tobias-liaudat/ClassG_amp/Fuente SW/fuente_negativa/imgs/PCB_neg_f.png

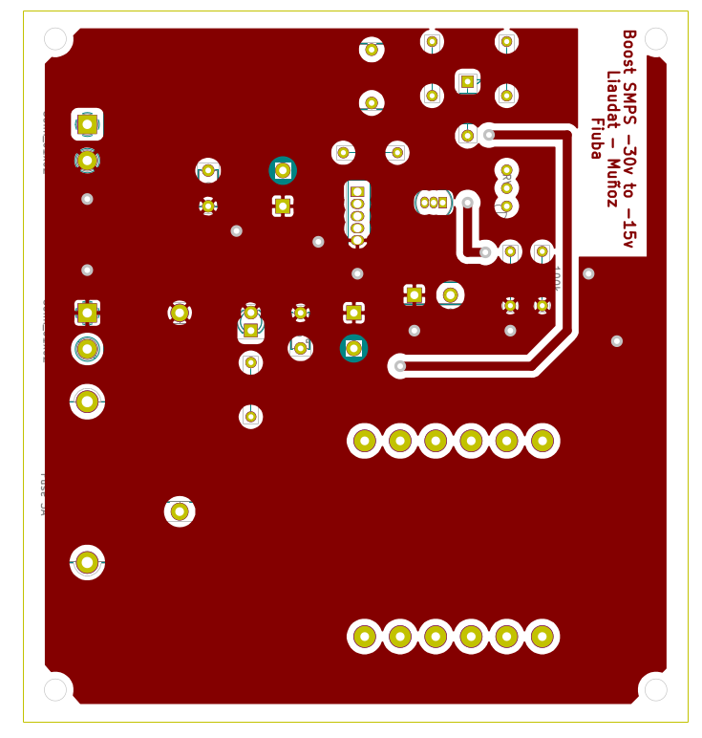
Fuente SW/fuente_negativa/imgs/PCB_neg_f.png
