tobias-liaudat/ClassG_amp/Amplificador/Ajustes_ganancia_alimentacion/ClassG_DEF_v3.asc

C1: cap; 47µ
C2: cap; 0.3n
C3: cap; 100µ
C4: cap; 47µ
C5: cap; 47µ
C6: cap; 100n
C7: cap; 100n
C8: cap; 1m
C9: cap; 30p
C10: cap; 1m
C11: cap; 100n
C12: cap; 47µ
C13: cap; 220µ
C14: cap; 220µ
C15: cap; 100n
C16: cap; 220µ
C17: cap; 220µ
C18: cap; {C_sUp}
D1: diode; 1N4148
D2: diode; 1N4148
D3: diode; 1N4148
D4: diode; 1N4148
D8: zener; D1N4728
D9: zener; D1N4728
D10: diode; 1N4148
D11: diode; 1N4148
D12: diode; dmur860
D13: diode; dmur860
D17: diode; 1N4148
D18: diode; 1N4148
L1: ind; 1µ
m_VA: voltage; {VCC}; Rser=0.1
m_VB: voltage; {VCC1}; Rser=0.1
PR1: res; {PR1}
Q1: pnp; BC856A
Q2: pnp; BC856A
Q3: npn; BC846A
Q4: npn; BC846A
Q5: pnp; BC856A
Q6: pnp; BC856A
Q7: pnp; 2SA1837
Q8: npn; 2SC4793
Q9: npn; BC846A
Q10: npn; BC846A
Q11: npn; 2SC4793
Q14: npn; 2SC4793
Q15: pnp; 2SA1837
Q16: npn; 2SC4793
Q17: pnp; 2SA1837
Q18: npn; 2SC5200
Q19: npn; 2SC5200
Q20: pnp; 2SA1943
Q21: pnp; 2SA1943
Q22: npn; BC846A
Q23: npn; BC846A
Q24: npn; BC846A
Q25: npn; BC846A
Q26: npn; MPSA42
Q27: pnp; MPSA92
R1: res; 100k
R2: res; 10
R3: res; 1.2k
R4: res; 1.2k
R5: res; 100
R6: res; 68
R7: res; 100
R8: res; 68
R9: res; 100
R10: res; 100
R11: res; 2.2k
R12: res; 2.2k
R13: res; 10k
R14: res; 10k
R15: res; 50
R16: res; 2.2k
R17: res; 2.2k
R18: res; 33
R19: res; 10
R20: res; 100
R21: res; 3.3K
R22: res; 390
R23: res; 16
R24: res; 2.2k
R25: res; 2.2k
R26: res; 10
R27: res; 10
R28: res; 100
R29: res; 100
R30: res; 560
R31: res; 180
R32: res; 100
R33: res; 100
R36: res; 100
R37: res; 0.22
R38: res; 2.2k
R39: res; 10
R40: res; 0.22
R41: res; 2.2k
R44: res; 0.01
R45: res; 330
R46: res; 100
R_FB_POT: res; {R_FB_POT}
RL: res; {RL}
S1: sw
V1: signal; SINE(0 {Vi} {freq})
V2: signal; PULSE(-1 10 20m 1n 1n 2m 4m)
VA: voltage; {VCC}; Rser=0.1
VB: voltage; {VCC1}; Rser=0.1
Named nets: 0, Vout, Vin, Vout2, m_VB, VB, VA, m_VA
Proteccion VAS
Degenracion emisor y muestreo para proteccion
VAS
Speedup capacitor
Current protection
Current protection
Vout
.meas tran Pmed_fuentes_neg AVG ((V(m_va)*(I(M_va)))+(V(m_vb)*(I(M_vb))))
.meas tran Pmed_fuentes_pos AVG (V(va)*(-I(Va)))+(V(vb)*(-I(Vb)))
.meas Pmed_F param (Pmed_fuentes_pos + Pmed_fuentes_neg)
Calculo potencias y eficiencia
.meas tran Pmed_RL AVG (V(vout)*(-I(Rl)))
.meas Eff param (Pmed_RL / Pmed_F)
; Simulaciones para las THD 
; .step param Vi list 1.74 1.27
.param Vi 1.0
; .step param freq list 1k 10k 20k
.param freq 1k
.param ciclos=15
.param puntos=10000
.param paso='1/(freq*puntos)' ; paso temporal
.param tf='ciclos/freq + 1m' ; Tiempo final
.tran 0 {tf} 1m {paso} ; Simulacion transient
.four {freq} 40 V(vout) ; Fourier
; .op
; Parametros
.param VCC 50 ; Riel alto
;.step param VCC list  30 40 50; Riel alto
.param VCC1 15 ; Riel bajo
.param PR1 0.22k ;   Pot MultV_BE
; .step param PR1 list 0.58k 0.59k 0.6k
.param R_FB_POT 10.6 ; Feedback R (Gain adjust)
.param RL 8 ; Carga
.param C_sUp 100n ; Cap SpeedUp
; Includes 
.inc D1N4728.mod
.inc DMBR1645.mod
.inc 2SC5200.mod
.inc 2SA1943.mod
.inc MUR860.LIB
.inc MPSA42.mod
.inc MPSA92.mod
.inc D1N5226.mod
.model SW SW()
Potenciometro 100 Ohm , 25 vueltas
Potenciometro 1 kOhm , 25 vueltas
.meas tran P_Q19 AVG((V(n012)-V(n020))*-Ie(Q19))
.meas tran P_Q18 AVG((V(va)-V(n012))*-Ie(Q18))
.meas tran P_Q16 AVG((V(va)-V(n009))*-Ie(Q16))
.meas tran P_Q14 AVG((V(va)-V(n017))*-Ie(Q14))
.meas tran P_Q20 AVG((V(n036)-V(n047))*Ie(Q20))
.meas tran P_Q21 AVG((V(n047)-V(m_VA))*Ie(Q21))
.meas tran P_Q15 AVG((V(n033)-V(m_VA))*Ie(Q15))
.meas tran P_Q17 AVG((V(n048)-V(m_VA))*Ie(Q17))
.meas tran P_Q7 AVG((V(n002)-V(n006))*Ie(Q7))
.meas tran P_Q11 AVG((V(n049)-V(n055))*-Ie(Q11))
.meas tran P_Q8 AVG((V(n013)-V(n018))*-Ie(Q8))
Realimentador
