tobias-liaudat/ClassG_amp/Fuente SW/fuente_positiva/simulacion/step_down_LM2576.asc

C1: polcap; 220µ; V=63 Irms=465m Rser=0.2 Lser=0 mfg="Nichicon" pn="UPR1J221MPH" type="Al electrolytic"
C2: polcap; 220µ; V=63 Irms=1.45 Rser=0.07 Lser=0 mfg="Panasonic" pn="ECA1JFQ471" type="Al electrolytic"
D1: schottky; MBR20100CT
D2: zener; BZX84C15L
D3: diode
I1: current; SINE(0.7 0.5 5k)
L1: ind; 33µ; Ipk=10.3 Rser=0.0023 Rpar=3108.6 Cpar=0 mfg="Coilcraft" pn="VER2923-333"
Q1: npn; BC548C
R1: res; 11k
R2: res; 1k
R3: res; 7
R4: res; 330
R5: res; 20k
R6: res; 20k
R7: res; 10k
R8: res; 180
R9: res; 1k
S1: sw
S2: sw
S3: sw
S4: sw
U1: LM2576_TRANS
V1: voltage; 30; Rser=0.1
V2: voltage; PWL(0 -1 {T_RL} 2m {T_RL2} -1m)
V3: voltage; 12
V4: voltage; PWL(0 -1 {T_F2} 1)
V5: voltage; PWL(0 -1 {T_SC} 1)
Named nets: 0, Vin, rel_GND, Q_Vout, V_FB, V_ON_OFF, Vout
.inc LM2576_TRANS.LIB
.inc 1N5822.mod
.tran 50m startup uic
.model SW SW()
.inc 1N4744.mod
.param T_F2 300m*2
.param T_RL 20m
.param T_RL2 30m
.param T_SC 100m*2
.inc MUR860.LIB
Fuente de switching positiva: Topología buck
