tobias-liaudat/ClassG_amp/Amplificador/claseG_mejoras/sin_limitador_corriente/ClassG_DS_test1.asc

C1: cap; 47µ
C2: cap; 1n
C3: cap; 47µ
C4: cap; 47µ
C5: cap; 47µ
C6: cap; 100n
C7: cap; 100n
C8: cap; 1m
C9: cap; 100p
C10: cap; 1m
C11: cap; 100n
C12: cap; 47µ
C13: cap; 220µ
C14: cap; 220µ
C15: cap; 100n
C16: cap; 220µ
C17: cap; 220µ
C18: cap; {C_sUp}
D1: diode; 1N4148
D2: diode; 1N4148
D3: diode; 1N4148
D4: diode; 1N4148
D8: zener; D1N4728
D9: zener; D1N4728
D10: diode; 1N4148
D11: diode; 1N4148
D12: diode; DMBR1645
D13: diode; DMBR1645
L1: ind; 1µ
m_VA: voltage; {VCC}
m_VB: voltage; {VCC1}
PR1: res; {PR1}
Q1: pnp; MPSA56
Q2: pnp; MPSA56
Q3: npn; MPSA06
Q4: npn; MPSA06
Q5: pnp; MPSA56
Q6: pnp; MPSA56
Q7: pnp; MPSA56
Q8: npn; MJE340
Q9: npn; MPSA06
Q10: npn; MPSA06
Q11: npn; MPSA06
Q14: npn; BD139
Q15: pnp; BD140
Q16: npn; BD139
Q17: pnp; BD140
Q18: npn; 2SC3281
Q19: npn; 2SC3281
Q20: pnp; Q2SA1302
Q21: pnp; Q2SA1302
Q22: npn; MPSA06
Q23: npn
Q24: npn; MPSA06
Q25: npn; MPSA06
Q26: npn; 2SC3281
Q27: npn; 2SC3281
Q28: pnp; Q2SA1302
Q29: pnp; Q2SA1302
R1: res; 100k
R2: res; 10
R3: res; 1.1k
R4: res; 1.1k
R5: res; 100
R6: res; 68
R7: res; 100
R8: res; 68
R9: res; 100
R10: res; 100
R11: res; 2.2k
R12: res; 2.2k
R13: res; 10k
R14: res; 10k
R15: res; 110
R16: res; 2.2k
R17: res; 2.2k
R18: res; 68
R19: res; 10
R20: res; 100
R21: res; 3.3K
R22: res; 680
R23: res; 16
R24: res; 2.2k
R25: res; 2.2k
R26: res; 10
R27: res; 10
R28: res; 100
R29: res; 100
R32: res; 100
R33: res; 100
R36: res; 100
R37: res; 0.1
R38: res; 2.2k
R39: res; 10
R40: res; 0.1
R41: res; 2.2k
R42: res; 100
R43: res; 0.1
R44: res; 0.1
R45: res; 100
RL: res; 8
V1: signal; SINE(0 1.5 20K)
VA: voltage; {VCC}
VB: voltage; {VCC1}
Named nets: 0, Vout, Vin, Vout2
.inc DMBR1645.mod
.inc D1N4728.mod
.four 20k 40 V(vout)
.options plotwinsize=0
.options numdgt=7
Proteccion VAS
Degenracion emisor y muestreo para proteccion
VAS
.tran 0 4m 1m 0.01u
Speedup capacitor
.param VCC 50
.param VCC1 15
.param C_sUp 100n
.param PR1 0.3k
