tobias-liaudat/ClassG_amp/Fuente SW/fuente_negativa/simulacion_alternativa/inverter_stepdown_LM2576.asc

C1: cap; 220µ
C2: cap; 220µ
D1: zener; BZX84C15L
D2: schottky; MBR20100CT
I1: current; PWL(6m 0.01 15m 1)
L1: ind; 22µ; Ipk=10.1 Rser=0.02752 Cpar=0
Q1: npn; BC548C
R1: res; 20k
R2: res; 20k
R3: res; 10k
R4: res; 24.63k
R5: res; 2.2k
R6: res; 30
R7: res; 330
S1: sw
S2: sw
S3: sw
S4: sw
U2: LM2576_TRANS
V1: voltage; 30
V2: voltage; 12
V3: voltage; PWL(1n -1 {T_F2} 1)
V4: voltage; PWL(1n -1 {T_RL} 1)
V5: voltage; PWL(1n -1 {T_SC} 1)
Named nets: 0, Vin, V_ON_OFF, Q_Vout, V_FB, Vout
.model SW SW()
.inc LM2576_TRANS.LIB
.inc 1N5822.mod
.tran 200m startup uic
.inc 1N4744.mod
.param T_F2 500m*2
.param T_RL 6m*2
.param T_SC 500m*2
22u
220u
